LydByDissing/stroem/docs/source/_static/android-chrome-192x192.png

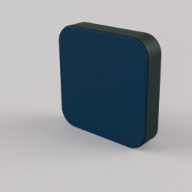
docs/source/_static/android-chrome-192x192.png
