LydByDissing/stroem/voicing/modal-analysis.png

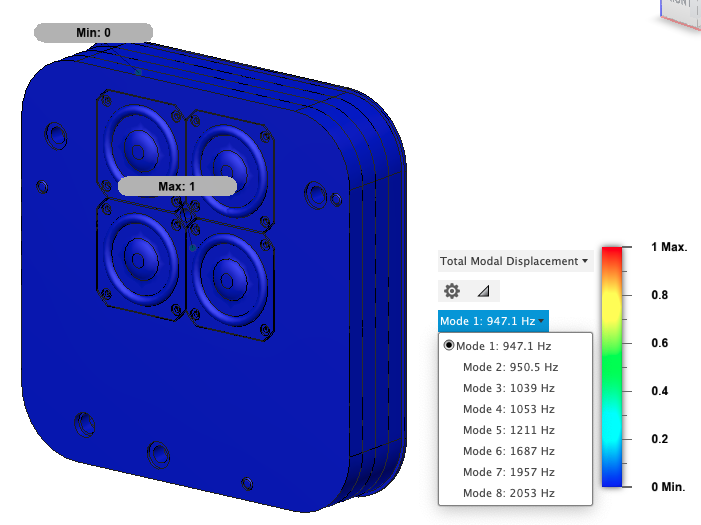
voicing/modal-analysis.png
